FPGA-Computer/component_tester/firmware/Markus/Not used/ST7565R.c

/* ************************************************************************
 *
 *   driver functions for ST7565R compatible grafic displays
 *   - 128 x 64 (132 x 64) pixels
 *   - SPI interface (4 and 5 line)
 *
 *   (c) 2015-2017 by Markus Reschke
 *
 * ************************************************************************ */

/*
 *  hints:
 *  - pin assignment for SPI
 *    /CS1        LCD_CS (optional)
 *    /RES        LCD_RESET (optional)
 *    A0          LCD_A0
 *    SCL (DB6)   LCD_SCL / SPI_SCK
 *    SI (DB7)    LCD_SI / SPI_MOSI
 *    For hardware SPI LCD_SCL and LCD_SI have to be the MCU's SCK and
 *    MOSI pins.
 *  - max. SPI clock rate: 20MHz
 *  - write only
 *  - horizontal flip might require an offset of 4 dots
 *    (132 RAM dots - 128 real dots = 4)
 */


/* local includes */
#include "config.h"           /* global configuration */

#ifdef LCD_ST7565R


/*
 *  local constants
 */

/* source management */
#define LCD_DRIVER_C


/*
 *  include header files
 */

/* local includes */
#include "common.h"           /* common header file */
#include "variables.h"        /* global variables */
#include "functions.h"        /* external functions */
#include "ST7565R.h"          /* ST7565R specifics */

/* fonts and symbols */
/* vertically aligned, vertical bit order flipped, bank-wise grouping */
#include "font_8x8_vf.h"
#include "symbols_24x24_vfp.h"



/*
 *  derived constants
 */

/* pages/bytes required for character's height */
#define CHAR_PAGES       ((FONT_SIZE_Y + 7) / 8)

/* number of lines and characters per line */
#define LCD_CHAR_X       (LCD_DOTS_X / FONT_SIZE_X)
#define LCD_CHAR_Y       ((LCD_DOTS_Y / 8) / CHAR_PAGES)

/* component symbols */
#ifdef SW_SYMBOLS
  /* pages/bytes required for symbol's height */
  #define SYMBOL_PAGES        ((SYMBOL_SIZE_Y + 7) / 8)

  /* size in relation to a character */
  #define LCD_SYMBOL_CHAR_X   ((SYMBOL_SIZE_X + FONT_SIZE_X - 1) / FONT_SIZE_X)
  #define LCD_SYMBOL_CHAR_Y   ((SYMBOL_SIZE_Y + CHAR_PAGES * 8 - 1) / (CHAR_PAGES * 8))

  /* check y size: we need at least 2 lines */
  #if LCD_SYMBOL_CHAR_Y < 2
    #error <<< Symbols too small! >>>
  #endif
#endif



/*
 *  local variables
 */

/* position management */
uint8_t             X_Start;       /* start position X (column) */
uint8_t             Y_Start;       /* start position Y (page) */

#ifdef SW_SYMBOLS
/* symbol positions (aligned to character positions) */
uint8_t             SymbolTop;     /* top line */
uint8_t             SymbolBottom;  /* bottom line */
uint8_t             SymbolLeft;    /* left of symbol */
uint8_t             SymbolRight;   /* right of symbol */
#endif



/* ************************************************************************
 *   low level functions for SPI interface
 * ************************************************************************ */


#ifdef LCD_SPI


/*
 *  set up interface bus
 *  - should be called at firmware startup
 */

void LCD_BusSetup(void)
{
  uint8_t           Bits;          /* bitmask */


  /*
   *  set control signals
   */

  Bits = LCD_DDR;                  /* get current directions */

  /* basic output pins */
  Bits |= (1 << LCD_A0);           /* A0 */

  /* optional output pins */
  #ifdef LCD_RESET
    Bits |= (1 << LCD_RESET);      /* /RES */
  #endif
  #ifdef LCD_CS
    Bits |= (1 << LCD_CS);         /* /CS1 */
  #endif

  LCD_DDR = Bits;                  /* set new directions */

  /* set default levels */
  #ifdef LCD_CS
    /* disable chip */
    LCD_PORT |= (1 << LCD_CS);     /* set /CS1 high */
  #endif

  #ifdef LCD_RESET
    /* disable reset */
    LCD_PORT |= (1 << LCD_RESET);  /* set /RES high */
  #endif


  /*
   *  init SPI bus
   */

  #ifdef SPI_HARDWARE
  /*
   *  set SPI clock rate (max. 20MHz)
   *  - max. MCU clock 20MHz / 2 = 10MHz
   *  - f_osc/2 (SPR1 = 0, SPR0 = 0, SPI2X = 1)
   */

  SPI.ClockRate = SPI_CLOCK_2X;    /* set clock rate flags */
  #endif

  SPI_Setup();                     /* set up SPI bus */
}



/*
 *  send a command to the LCD
 *
 *  requires:
 *  - byte value to send
 */
 
void LCD_Cmd(uint8_t Cmd)
{
  /* indicate command mode */
  LCD_PORT &= ~(1 << LCD_A0);      /* set A0 low */

  /* select chip, if pin available */
  #ifdef LCD_CS
    LCD_PORT &= ~(1 << LCD_CS);    /* set /CS1 low */
  #endif

  SPI_Write_Byte(Cmd);             /* write command byte */

  /* deselect chip, if pin available */
  #ifdef LCD_CS
    LCD_PORT |= (1 << LCD_CS);     /* set /CS1 high */
  #endif
}



/*
 *  send data to the LCD
 *
 *  requires:
 *  - byte value to send
 */

void LCD_Data(uint8_t Data)
{
  /* indicate data mode */
  LCD_PORT |= (1 << LCD_A0);       /* set A0 high */

  /* select chip, if pin available */
  #ifdef LCD_CS
    LCD_PORT &= ~(1 << LCD_CS);    /* set /CS1 low */
  #endif

  SPI_Write_Byte(Data);            /* write data byte */

  /* deselect chip, if pin available */
  #ifdef LCD_CS
    LCD_PORT |= (1 << LCD_CS);     /* set /CS1 high */
  #endif
}

#endif



/* ************************************************************************
 *   high level functions
 * ************************************************************************ */


/*
 *  set LCD dot position
 *  - since we can't read the LCD and don't use a RAM buffer
 *    we have to move page-wise in y direction
 *  - top left: 0/0
 *
 *  requires:
 *  - x:  horizontal position (0-)
 *  - y:  vertical position (0-)
 */

void LCD_DotPos(uint8_t x, uint8_t y)
{
  uint8_t           Temp;     /* temp. value */

  /* horizontal position (column) */
  Temp = x;
  Temp &= 0b00001111;              /* filter lower nibble */
  LCD_Cmd(CMD_COLUMN_L | Temp);    /* set lower nibble */
  Temp = x;
  Temp >>= 4;                      /* shift upper nibble to lower */
  Temp &= 0b00001111;              /* filter nibble */
  LCD_Cmd(CMD_COLUMN_H | Temp);    /* set upper nibble */

  /* vertical position (page) */
  LCD_Cmd(CMD_PAGE | y);           /* set page */
}



/*
 *  set LCD character position
 *  - since we can't read the LCD and don't use a RAM buffer
 *    we have to move page-wise in y direction
 *  - top left: 1/1
 *
 *  requires:
 *  - x:  horizontal position (1-)
 *  - y:  vertical position (1-)
 */

void LCD_CharPos(uint8_t x, uint8_t y)
{
  /* update UI */
  UI.CharPos_X = x;
  UI.CharPos_Y = y;

  /* update display */

  /* horizontal position (column) */
  x--;                             /* columns start at 0 */
  x *= FONT_SIZE_X;                /* offset for character */
  #ifdef LCD_OFFSET_X
  x += 4;                          /* x offset of 4 dots */
  #endif
  X_Start = x;                     /* update start position */

  /* vertical position (page) */
  y--;                             /* pages start at 0 */
  y *= CHAR_PAGES;                 /* offset for character */
  Y_Start = y;                     /* update start position */

  LCD_DotPos(x, y);                /* set dot position */
}



/*
 *  clear one single character line
 *
 *  requires:
 *  - Line: line number (1-)
 *    special case line 0: clear remaining space in current line
 */ 

void LCD_ClearLine(uint8_t Line)
{
  uint8_t           MaxPage;            /* page limit */
  uint8_t           n = 1;              /* counter */

  if (Line == 0)         /* special case: rest of current line */
  {
    Line = UI.CharPos_Y;      /* get current line */
    n = UI.CharPos_X;         /* get current character position */
  }

  LCD_CharPos(n, Line);       /* set char position */

  /* calculate pages */
  Line = Y_Start;                       /* get start page */
  MaxPage = Line + CHAR_PAGES;          /* end page + 1 */

  /* clear line */
  while (Line < MaxPage)           /* loop through pages */
  {
    LCD_DotPos(X_Start, Line);     /* set dot position */

    /* clear page */
    n = X_Start;              /* reset counter */
    while (n < 132)           /* up to internal RAM size */
    {
      LCD_Data(0);            /* send empty byte */
      n++;                    /* next byte */
    }

    Line++;                   /* next page */
  }
}



/*
 *  clear the display 
 */

void LCD_Clear(void)
{
  uint8_t           n = 1;         /* counter */

  /* we have to clear all dots manually :( */
  while (n <= LCD_CHAR_Y)          /* for all lines */
  {
    LCD_ClearLine(n);              /* clear line */
    n++;                           /* next line */
  }

  LCD_CharPos(1, 1);          /* reset character position */
}



/*
 *  set contrast
 *  required:
 *  - value: 0-63
 */

void LCD_Contrast(uint8_t Contrast)
{
  if (Contrast <= 63)              /* limit value */
  {
    /* set contrast */
    LCD_Cmd(CMD_V0_MODE);          /* set command */
    LCD_Cmd(Contrast);             /* contrast value */

    NV.Contrast = Contrast;        /* update value */
  }
}



/*
 *  initialize LCD
 *  - for a single 3.3V supply
 */
 
void LCD_Init(void)
{
  #ifdef LCD_RESET
  /* reset display */
  LCD_PORT &= ~(1 << LCD_RESET);        /* set /RES low */
  wait1us();                            /* wait 1µs */
  LCD_PORT |= (1 << LCD_RESET);         /* set /RES high */
  wait1us();                            /* wait 1µs */
  #endif

  /* set start line: user defined value (default 0) */
  LCD_Cmd(CMD_START_LINE | LCD_START_Y);

  /* set segment driver direction (ADC) */
  #ifdef LCD_FLIP_X
    LCD_Cmd(CMD_SEGMENT_DIR | FLAG_ADC_REVERSE);  /* flip horizontally */
  #else  
    LCD_Cmd(CMD_SEGMENT_DIR | FLAG_ADC_NORMAL);   /* normal */
  #endif

  /* set common driver direction */
  #ifdef LCD_FLIP_Y
    LCD_Cmd(CMD_COMMON_DIR | FLAG_COM_REVERSE);   /* flip vertically */
  #else
    LCD_Cmd(CMD_COMMON_DIR | FLAG_COM_NORMAL);    /* normal */
  #endif

  /* set LCD bias to 1/9 (duty 1/65) */
  LCD_Cmd(CMD_LCD_BIAS | FLAG_BIAS_19);

  /* set power mode: all on */
  LCD_Cmd(CMD_POWER_MODE | FLAG_FOLOWER_ON | FLAG_REGULATOR_ON | FLAG_BOOSTER_ON);

  /* set booster ratio to 4x */
  LCD_Cmd(CMD_BOOSTER_MODE);       /* set command */
  LCD_Cmd(FLAG_BOOSTER_234);       /* ratio */

  /* set contrast: resistor ratio 6.5 */
  LCD_Cmd(CMD_V0_RATIO | FLAG_RATIO_65);

  /* set contrast: default value */
  LCD_Contrast(LCD_CONTRAST);

  /* no indicator */
  LCD_Cmd(CMD_INDICATOR_MODE);     /* set command */
  LCD_Cmd(FLAG_INDICATOR_OFF);     /* mode */

  /* switch display on */
  LCD_Cmd(CMD_DISPLAY | FLAG_DISPLAY_ON);

  /* update maximums */
  UI.CharMax_X = LCD_CHAR_X;       /* characters per line */
  UI.CharMax_Y = LCD_CHAR_Y;       /* lines */
  UI.MaxContrast = 63;             /* LCD contrast */

  LCD_Clear();                /* clear display */
}



/*
 *  display a single character
 *
 *  requires:
 *  - Char: character to display
 */

void LCD_Char(unsigned char Char)
{
  uint8_t           *Table;        /* pointer to table */
  uint8_t           Index;         /* font index */
  uint16_t          Offset;        /* address offset */
  uint8_t           Page;          /* page number */
  uint8_t           x;             /* bitmap x byte counter */
  uint8_t           y = 1;         /* bitmap y byte counter */

  /* prevent x overflow */
  if (UI.CharPos_X > LCD_CHAR_X) return;

  /* get font index number from lookup table */
  Table = (uint8_t *)&FontTable;        /* start address */
  Table += Char;                        /* add offset for character */
  Index = pgm_read_byte(Table);         /* get index number */
  if (Index == 0xff) return;            /* no character bitmap available */

  /* calculate start address of character bitmap */
  Table = (uint8_t *)&FontData;        /* start address of font data */
  Offset = FONT_BYTES_N * Index;       /* offset for character */
  Table += Offset;                     /* address of character data */

  Page = Y_Start;                  /* get start page */

  /* read character bitmap and send it to display */
  while (y <= FONT_BYTES_Y)
  {
    LCD_DotPos(X_Start, Page);          /* set start position */

    /* read and send all column bytes for this row */
    x = 1;
    while (x <= FONT_BYTES_X)
    {
      Index = pgm_read_byte(Table);     /* read byte */
      LCD_Data(Index);                  /* send byte */
      Table++;                          /* address for next byte */
      x++;                              /* next byte */
    }

    Page++;                             /* next page */
    y++;                                /* next row */
  }

  /* update character position */
  UI.CharPos_X++;                  /* next character in current line */
  X_Start += FONT_SIZE_X;          /* also update X dot position */
}



/*
 *  set cursor
 *
 *  required:
 *  - Mode: cursor mode
 *    0: cursor on
 *    1: cursor off
 */

void LCD_Cursor(uint8_t Mode)
{
  LCD_CharPos(LCD_CHAR_X, LCD_CHAR_Y);       /* move to bottom right */

  if (Mode)              /* cursor on */
  {
    LCD_Char('>');
  }
  else                   /* cursor off */
  {
    LCD_Char(' ');
  }
}



/* ************************************************************************
 *   fancy stuff
 * ************************************************************************ */


#ifdef SW_SYMBOLS

/*
 *  display a component symbol
 *
 *  requires:
 *  - ID: symbol to display
 */

void LCD_Symbol(uint8_t ID)
{
  uint8_t           *Table;        /* pointer to symbol table */
  uint8_t           Data;          /* symbol data */
  uint16_t          Offset;        /* address offset */
  uint8_t           Page;          /* page number */
  uint8_t           x;             /* bitmap x byte counter */
  uint8_t           y = 1;         /* bitmap y byte counter */

  /* calculate start address of character bitmap */
  Table = (uint8_t *)&SymbolData;       /* start address of symbol data */
  Offset = SYMBOL_BYTES_N * ID;         /* offset for symbol */
  Table += Offset;                      /* address of symbol data */

  Page = Y_Start;                  /* get start page */

  /* read character bitmap and send it to display */
  while (y <= SYMBOL_BYTES_Y)
  {
    if (y > 1)                /* multi-page bitmap */
    {
      LCD_DotPos(X_Start, Page);        /* move to new page */
    }

    /* read and send all column bytes for this row */
    x = 1;
    while (x <= SYMBOL_BYTES_X)
    {
      Data = pgm_read_byte(Table);      /* read byte */
      LCD_Data(Data);                   /* send byte */
      Table++;                          /* address for next byte */
      x++;                              /* next byte */
    }

    Page++;                             /* next page */
    y++;                                /* next row */
  }

  /* hint: we don't update the char position */
}



/*
 *  display fancy probe number
 *
 *  requires:
 *  - Probe: probe number
 *  - Table: pointer to pinout details
 */

void LCD_FancyProbeNumber(uint8_t Probe, uint8_t *Table)
{
  uint8_t           Data;          /* pinout data */
  uint8_t           x;             /* x position */
  uint8_t           y;             /* y position */

  Data = pgm_read_byte(Table);     /* read pinout details */

  if (Data != PIN_NONE)            /* show pin */
  {
    /* determine position based on pinout data */
    x = SymbolLeft;         /* set default positions */
    y = SymbolTop;
    if (Data & PIN_RIGHT) x = SymbolRight;
    if (Data & PIN_BOTTOM) y = SymbolBottom;

    /* show probe number */
    LCD_CharPos(x, y);           /* set position */
    LCD_ProbeNumber(Probe);      /* display probe number */
  }
}



/*
 *  show fancy pinout for semiconductors
 *  - display a nice component symbol
 *    starting in next line, aligned to right side
 *  - display pin numbers left and right of symbol
 *  - symbol ID (0-) in Check.Symbol
 */

void LCD_FancySemiPinout(void)
{
  uint8_t           Line;          /* line number */
  uint8_t           x, y;          /* position of char */
  uint8_t           *Table;        /* pointer to pin table */
  uint16_t          Offset;        /* address offset */

  /* save current char position */
  x = UI.CharPos_X;        /* column */
  y = UI.CharPos_Y;        /* line */

  /* check for sufficient screen size */
  Line = y + 1;               /* next line */
  /* last line is reserved for cursor/touch bar */
  if (Line > (LCD_CHAR_Y - LCD_SYMBOL_CHAR_Y)) return;  /* too few lines */

  /* determine positions */
  SymbolTop = Line;                          /* top is current line */
  SymbolBottom = Line;
  SymbolBottom += (LCD_SYMBOL_CHAR_Y - 1);   /* plus symbol's height */
  SymbolRight = LCD_CHAR_X;                  /* align to right side */
  /* minus symbol's width and pin IDs */
  SymbolLeft = LCD_CHAR_X - LCD_SYMBOL_CHAR_X - 1;

  /* calculate start address of pinout details */
  Table = (uint8_t *)&PinTable;         /* start address of pin table */
  Offset = Check.Symbol * 3;            /* offset for pin details */
  Table += Offset;                      /* address of pin details */

  /* display probe numbers */
  LCD_FancyProbeNumber(Semi.A, Table);       /* A pin */
  Table++;                                   /* details for next pin */
  LCD_FancyProbeNumber(Semi.B, Table);       /* B pin */
  Table++;                                   /* details for next pin */
  LCD_FancyProbeNumber(Semi.C, Table);       /* C pin */

  /* display symbol */
  LCD_CharPos(SymbolLeft + 1, SymbolTop);    /* set top left position  */
  LCD_Symbol(Check.Symbol);                  /* display symbol */

  LCD_CharPos(x, y);          /* restore old char position */
}

#endif



/* ************************************************************************
 *   clean-up of local constants
 * ************************************************************************ */

/* source management */
#undef LCD_DRIVER_C

#endif

/* ************************************************************************
 *   EOF
 * ************************************************************************ */
